tlee10333/Eclectronics-USB/Eclectronics/3dshapes/DFN8_3x3_0.65.step

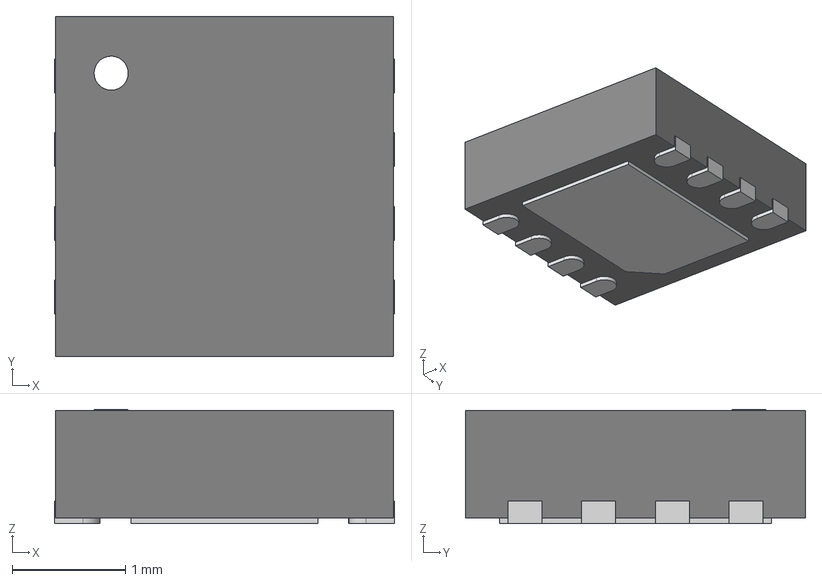
[picture p15: CAD file, 2026-04-13]
Eclectronics/3dshapes/DFN8_3x3_0.65.step
3.00 x 3.00 x 1.01 mm
