tlee10333/Eclectronics-USB/Eclectronics/3dshapes/RP2350A-QFN60.step

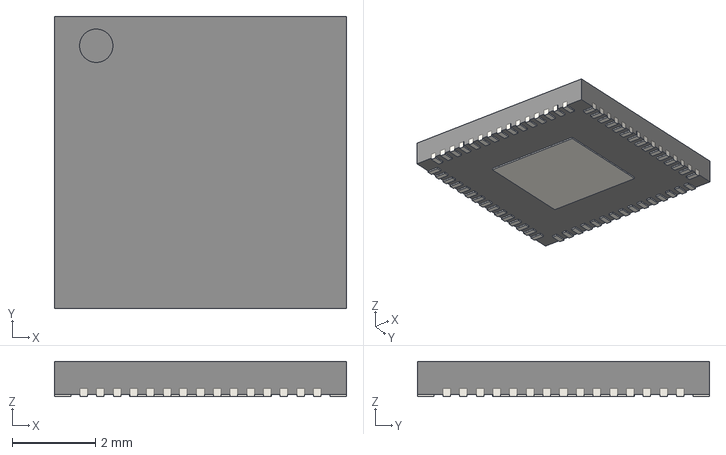
[picture p16: CAD file, 2026-04-13]
Eclectronics/3dshapes/RP2350A-QFN60.step
7.00 x 7.00 x 0.85 mm
