tlee10333/Eclectronics-USB/Eclectronics/3dshapes/BarrelJack.STEP

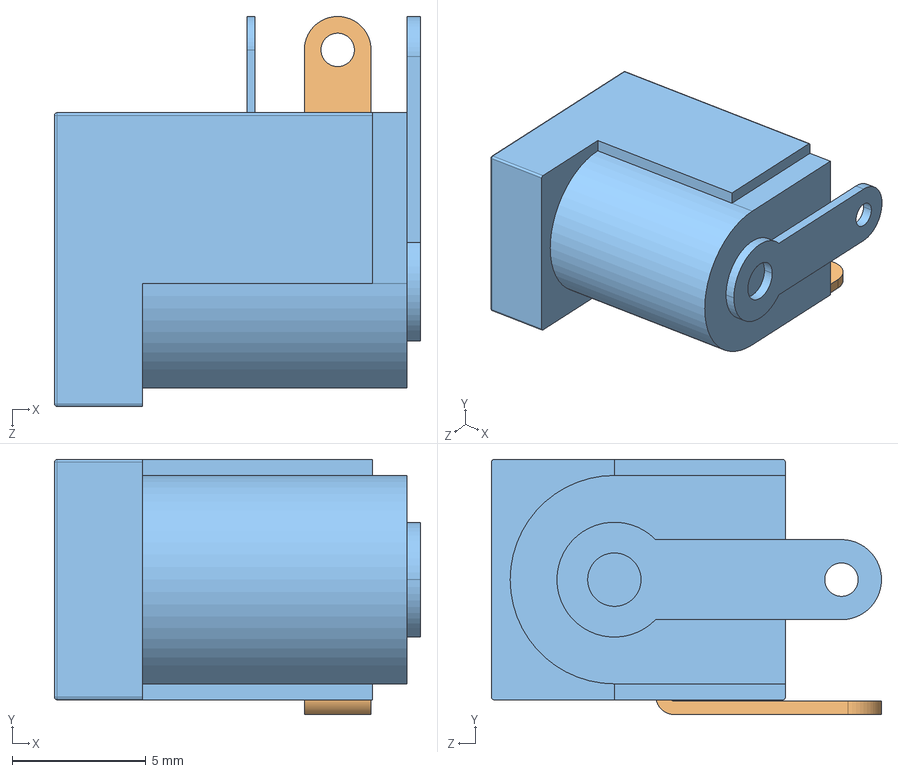
[picture p17: CAD file, 2026-04-13]
Eclectronics/3dshapes/BarrelJack.STEP
13.7 x 9.55 x 14.6 mm
