tlee10333/Eclectronics-USB/Eclectronics/3dshapes/WSON8-6x5.STEP

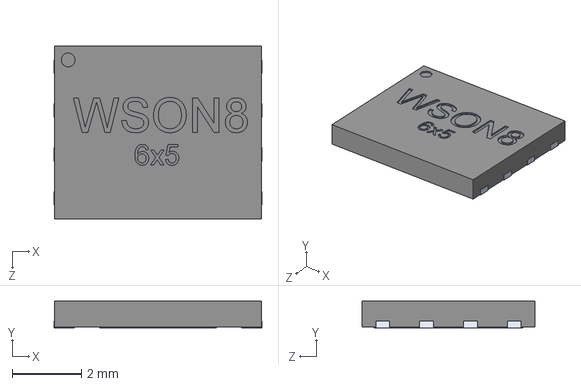
[picture p18: CAD file, 2026-04-13]
Eclectronics/3dshapes/WSON8-6x5.STEP
6.02 x 0.77 x 5.00 mm
