tlee10333/Eclectronics-USB/Eclectronics/3dshapes/RP2040_QFN_PACKAGE.STEP

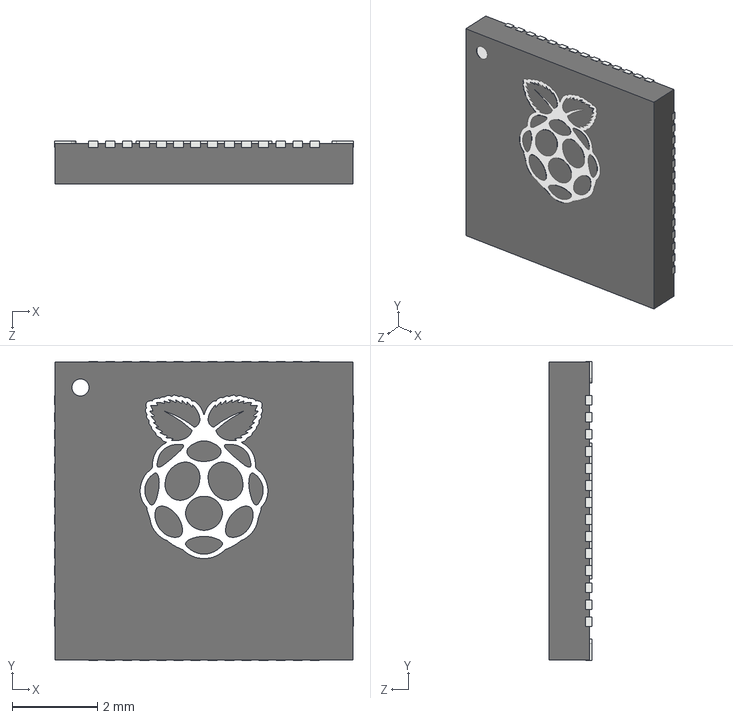
[picture p19: CAD file, 2026-04-13]
Eclectronics/3dshapes/RP2040_QFN_PACKAGE.STEP
7.02 x 7.02 x 1.00 mm
