tlee10333/Eclectronics-USB/Eclectronics/3dshapes/ABM10.STP

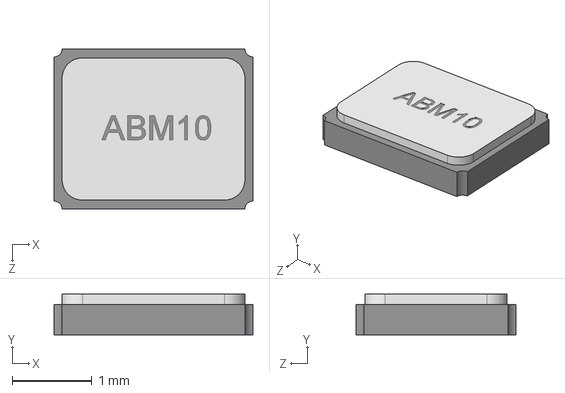
[picture p20: CAD file, 2026-04-13]
Eclectronics/3dshapes/ABM10.STP
2.49 x 0.508 x 2.01 mm
