tlee10333/Eclectronics-USB/Eclectronics/3dshapes/EEEFTH101XAL.step

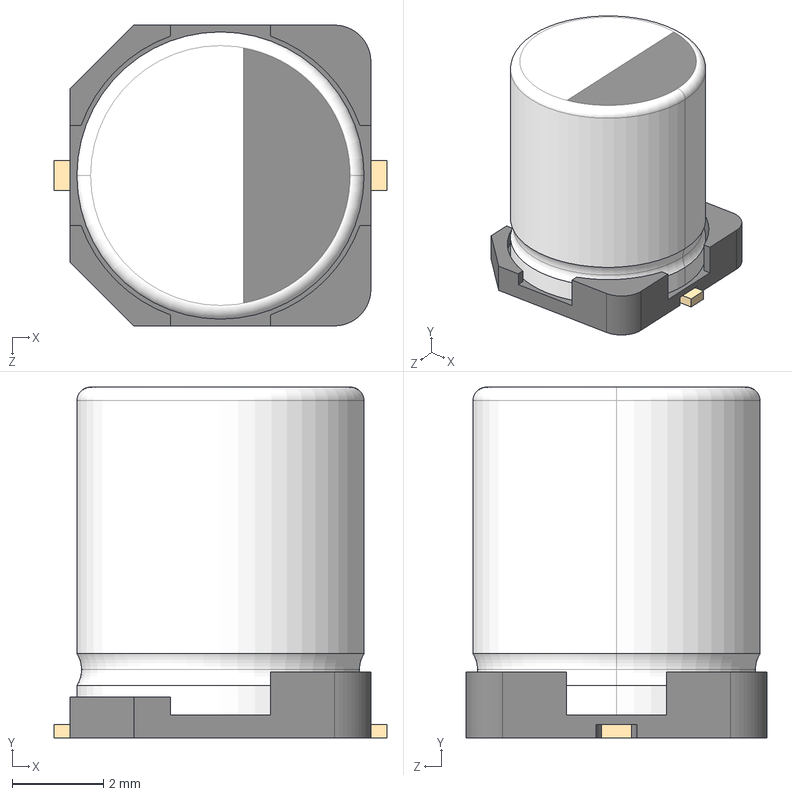
[picture p21: CAD file, 2026-04-13]
Eclectronics/3dshapes/EEEFTH101XAL.step
7.30 x 7.70 x 6.60 mm
