tlee10333/Eclectronics-USB/Eclectronics/3dshapes/IN-S85TATRGB.stp

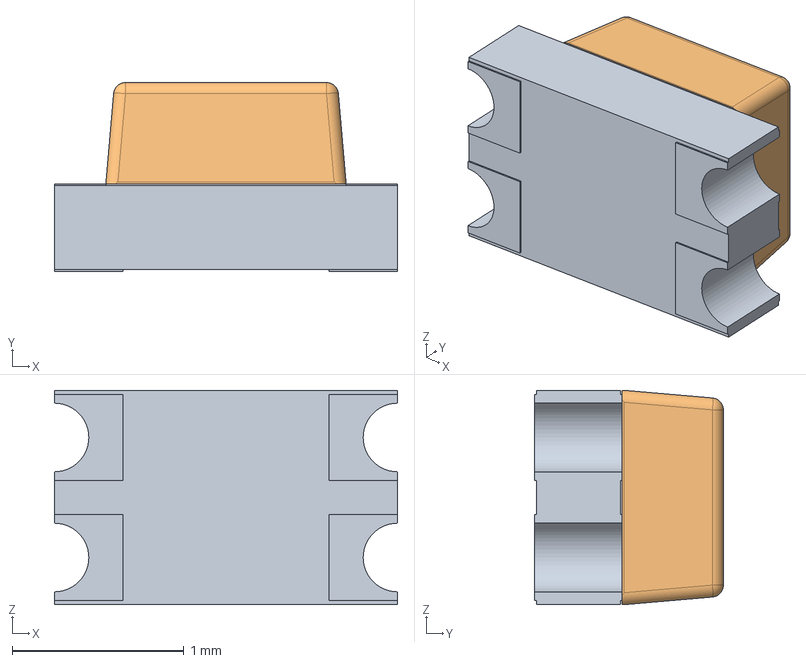
[picture p23: CAD file, 2026-04-13]
Eclectronics/3dshapes/IN-S85TATRGB.stp
2.00 x 1.10 x 1.25 mm
