tlee10333/Eclectronics-USB/Eclectronics/3dshapes/TL3301AFxxxxJ.stp

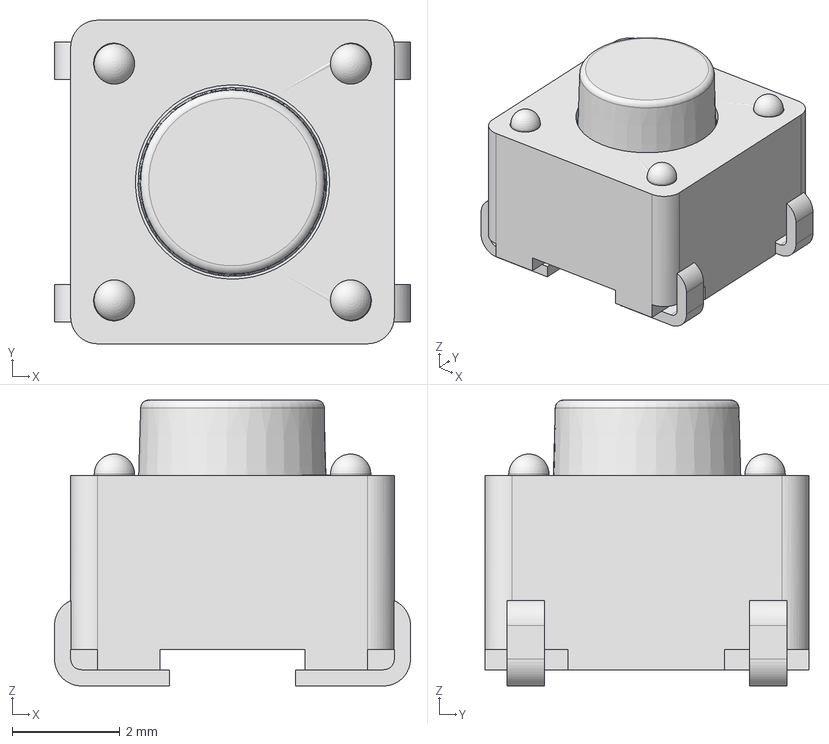
[picture p24: CAD file, 2026-04-13]
Eclectronics/3dshapes/TL3301AFxxxxJ.stp
6.60 x 6.00 x 5.30 mm
