tlee10333/Eclectronics-USB/Eclectronics/3dshapes/219-3M.STEP

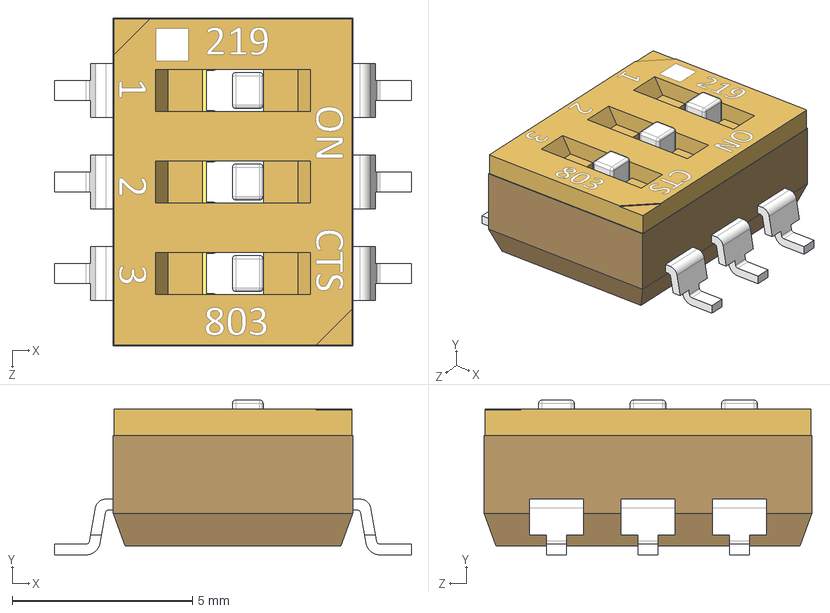
[picture p25: CAD file, 2026-04-13]
Eclectronics/3dshapes/219-3M.STEP
9.91 x 4.30 x 9.10 mm
