tlee10333/Eclectronics-USB/Eclectronics/3dshapes/KXT321LHS.stp

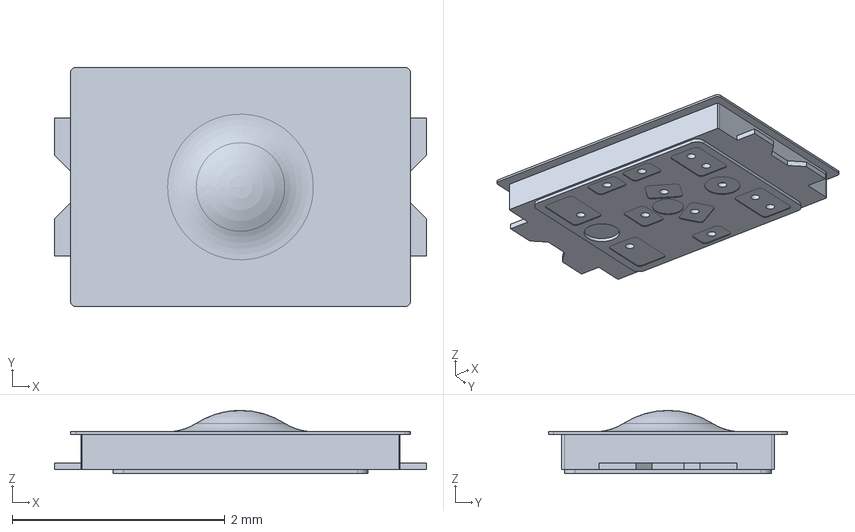
[picture p26: CAD file, 2026-04-13]
Eclectronics/3dshapes/KXT321LHS.stp
3.50 x 2.25 x 0.595 mm
