tlee10333/Eclectronics-USB/Eclectronics/3dshapes/usb4216-03-a.stp

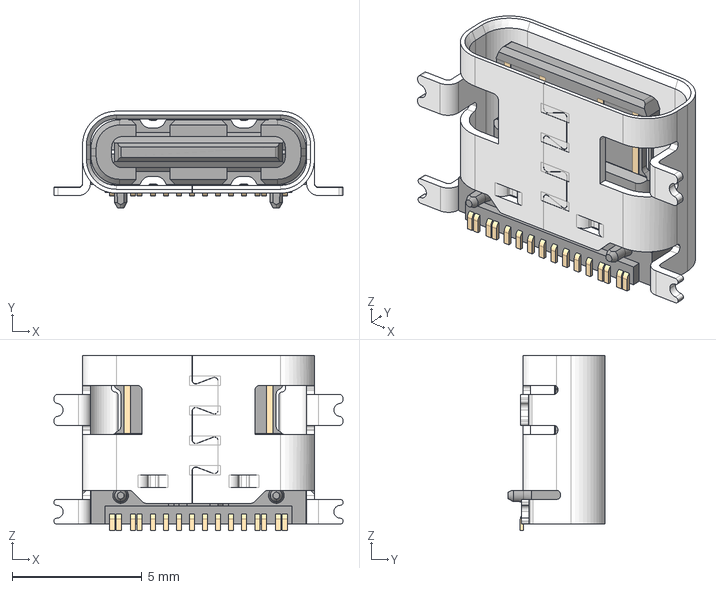
[picture p27: CAD file, 2026-04-13]
Eclectronics/3dshapes/usb4216-03-a.stp
11.1 x 3.73 x 6.75 mm
