tlee10333/Eclectronics-USB/Eclectronics/3dshapes/AOTA-B201610S3R3-101-T.stp

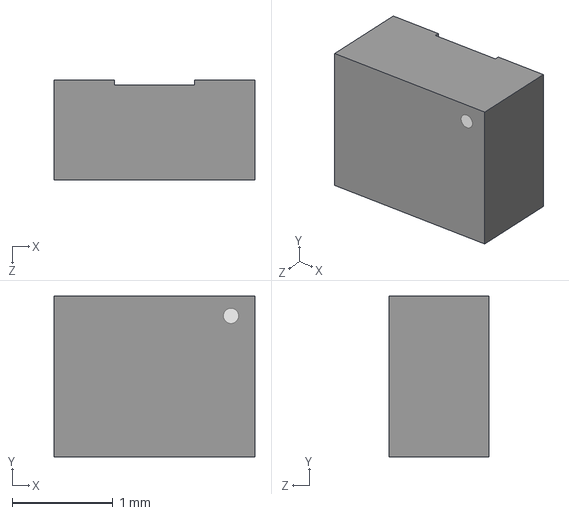
[picture p28: CAD file, 2026-04-13]
Eclectronics/3dshapes/AOTA-B201610S3R3-101-T.stp
2.00 x 1.60 x 1.00 mm
