tlee10333/Eclectronics-USB/Eclectronics/3dshapes/WS2812-2020.STEP

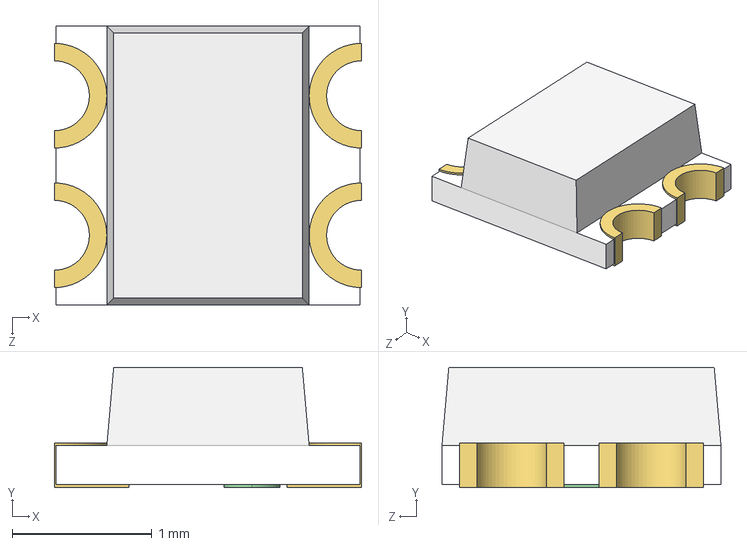
[picture p29: CAD file, 2026-04-13]
Eclectronics/3dshapes/WS2812-2020.STEP
2.20 x 0.86 x 2.00 mm
