tlee10333/Eclectronics-USB/Eclectronics/3dshapes/USB4505-03-0-A_REVA.step

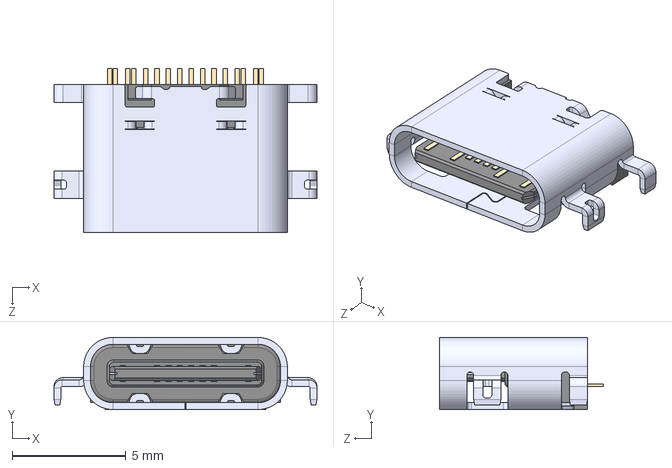
[picture p30: CAD file, 2026-04-13]
Eclectronics/3dshapes/USB4505-03-0-A_REVA.step
11.5 x 3.16 x 7.20 mm
