tlee10333/Eclectronics-USB/Eclectronics/3dshapes/B4B-XH-A.step

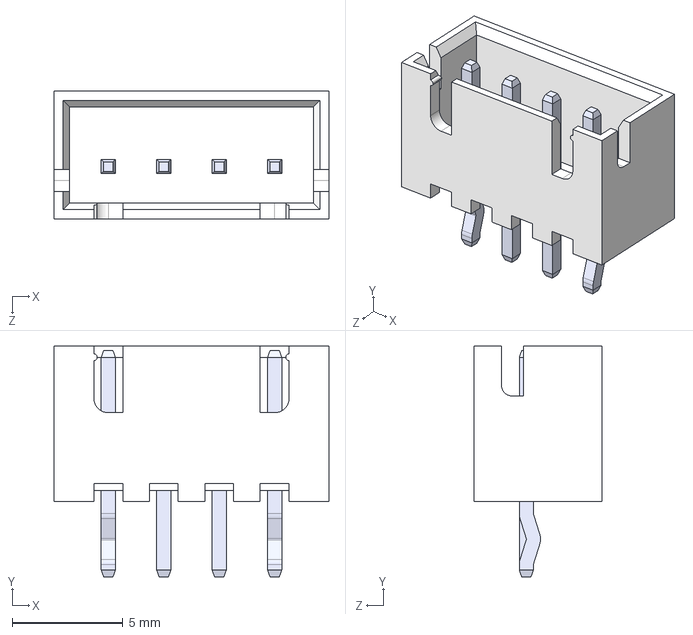
[picture p31: CAD file, 2026-04-13]
Eclectronics/3dshapes/B4B-XH-A.step
12.4 x 10.4 x 5.75 mm
