tlee10333/Eclectronics-USB/Eclectronics/3dshapes/RTE0020A.stp

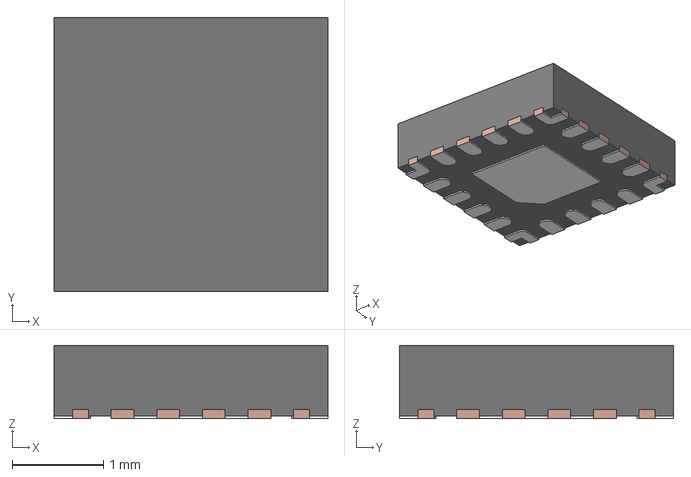
[picture p32: CAD file, 2026-04-13]
Eclectronics/3dshapes/RTE0020A.stp
3.00 x 3.00 x 0.8 mm
FRAME
