tlee10333/Eclectronics-USB/Eclectronics/3dshapes/ABM10-27.000MHZ-E20-T.step

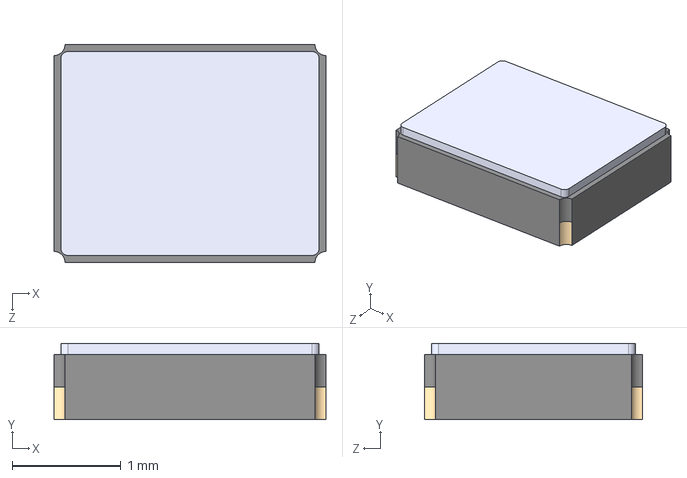
[picture p33: CAD file, 2026-04-13]
Eclectronics/3dshapes/ABM10-27.000MHZ-E20-T.step
2.50 x 0.7 x 2.00 mm
