tlee10333/Eclectronics-USB/Eclectronics/3dshapes/STP_831056289_rev1.stp

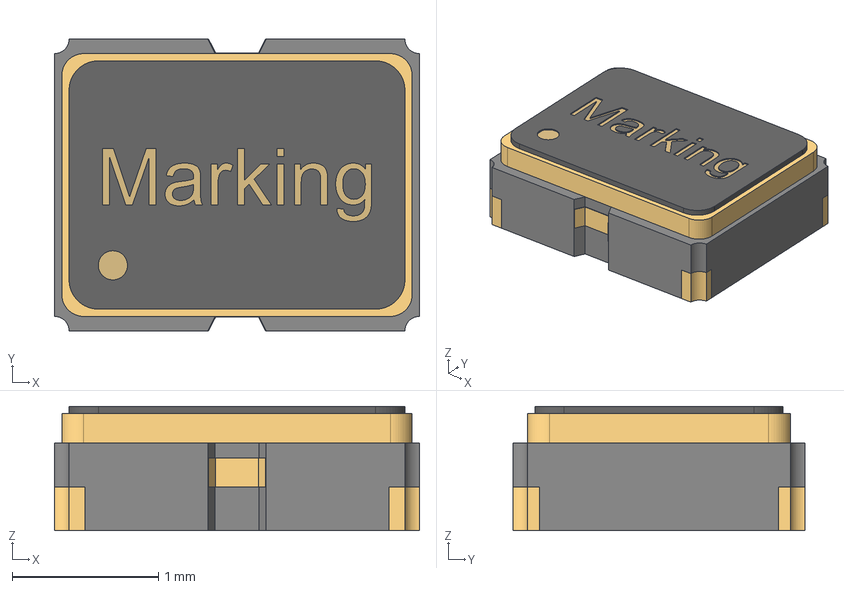
[picture p34: CAD file, 2026-04-13]
Eclectronics/3dshapes/STP_831056289_rev1.stp
2.50 x 2.00 x 0.85 mm
Pins
Cover
