tlee10333/Eclectronics-USB/Eclectronics/3dshapes/CSTNE.step

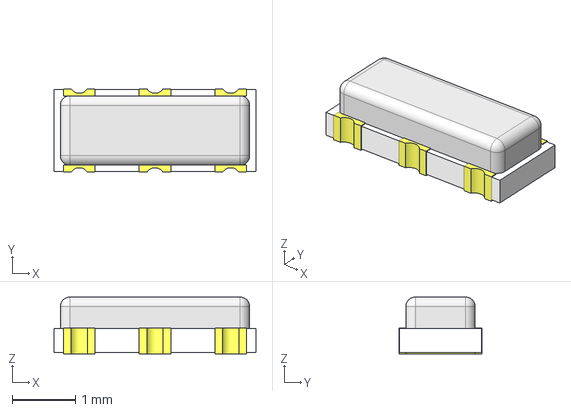
[picture p35: CAD file, 2026-04-13]
Eclectronics/3dshapes/CSTNE.step
3.20 x 1.32 x 0.9 mm
