tlee10333/Eclectronics-USB/Eclectronics/3dshapes/S4B-PH-SM4-TB.stp

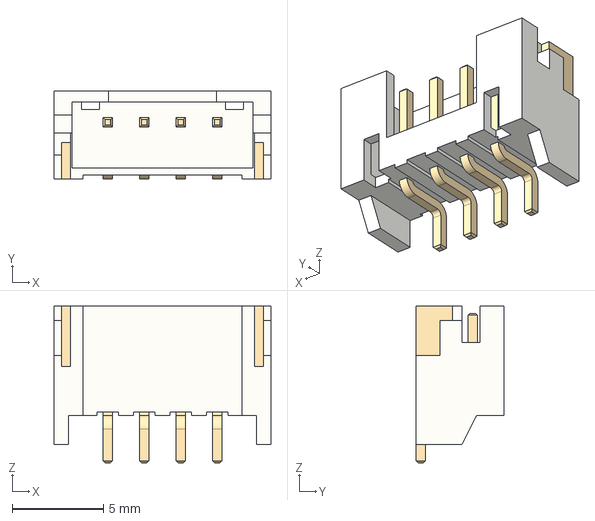
[picture p36: CAD file, 2026-04-13]
Eclectronics/3dshapes/S4B-PH-SM4-TB.stp
11.9 x 4.80 x 8.60 mm
