tlee10333/Eclectronics-USB/Eclectronics/3dshapes/PA5003.182NLT.step

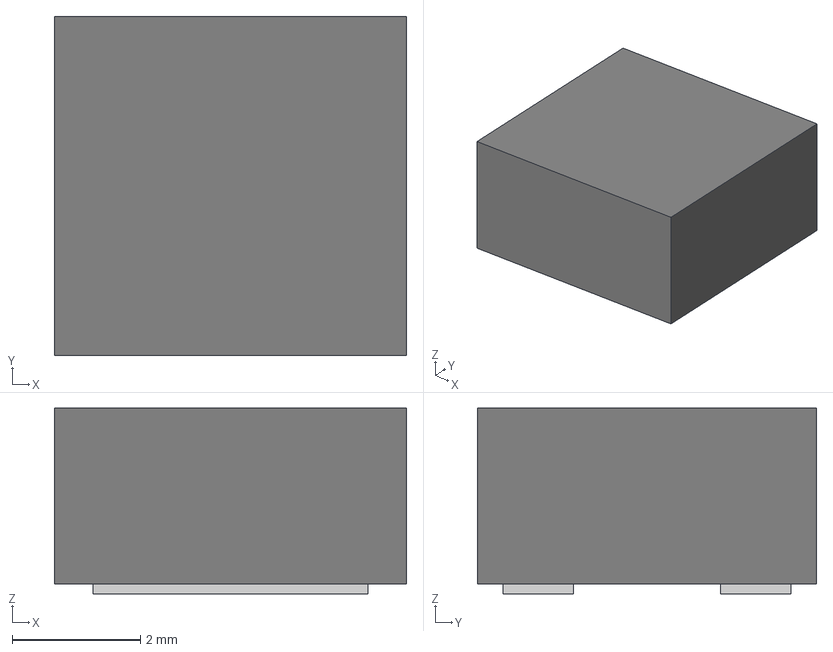
[picture p37: CAD file, 2026-04-13]
Eclectronics/3dshapes/PA5003.182NLT.step
5.50 x 5.30 x 2.90 mm
