tlee10333/Eclectronics-USB/Eclectronics/3dshapes/RNR0011A.stp

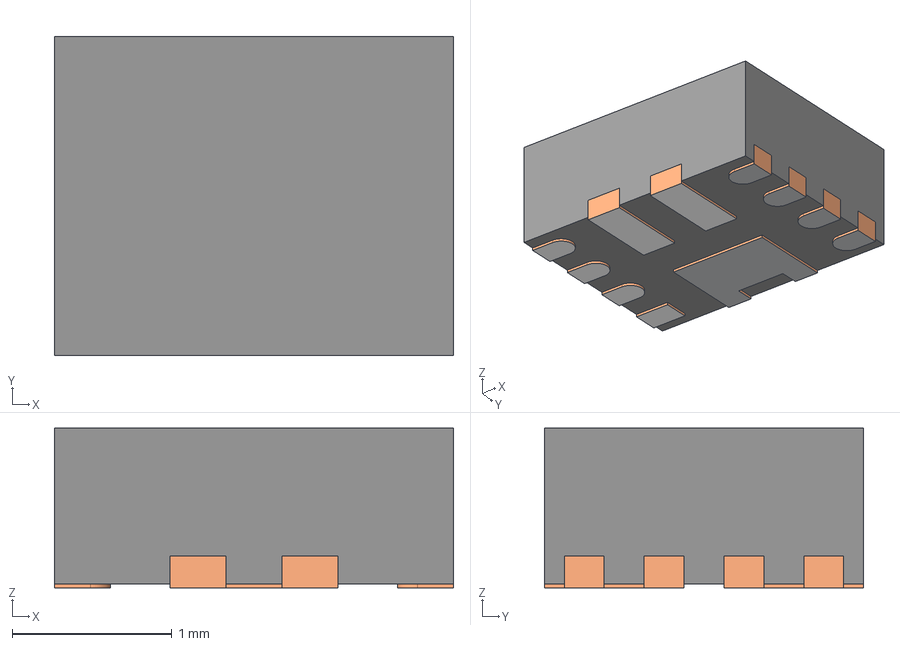
[picture p38: CAD file, 2026-04-13]
Eclectronics/3dshapes/RNR0011A.stp
2.50 x 2.00 x 1.00 mm
FRAME-RNR0011A
BODY-QFN
PIN1-ID
