tlee10333/Eclectronics-USB/Eclectronics/3dshapes/ABS06-107.STP

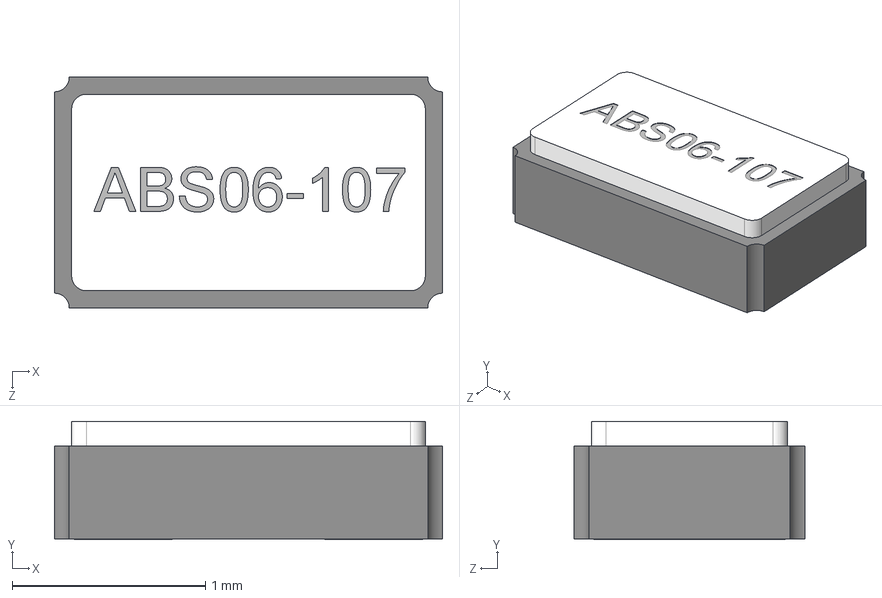
[picture p39: CAD file, 2026-04-13]
Eclectronics/3dshapes/ABS06-107.STP
2.01 x 0.612 x 1.19 mm
