tlee10333/Eclectronics-USB/Eclectronics/3dshapes/SJ-3524-SMT-TR-BE.step

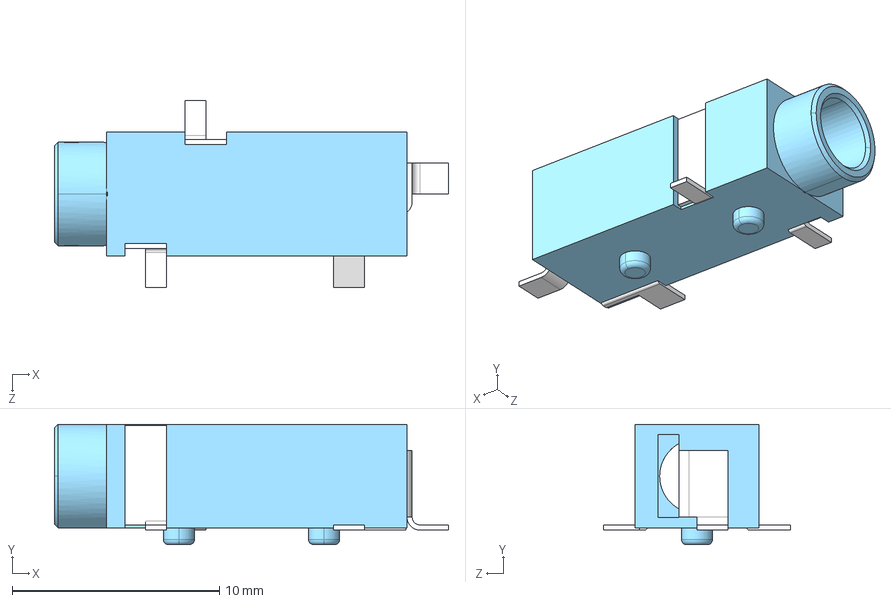
[picture p40: CAD file, 2026-04-13]
Eclectronics/3dshapes/SJ-3524-SMT-TR-BE.step
19.0 x 5.80 x 9.00 mm
