tlee10333/Eclectronics-USB/Eclectronics/3dshapes/3382g-001-xxx.stp

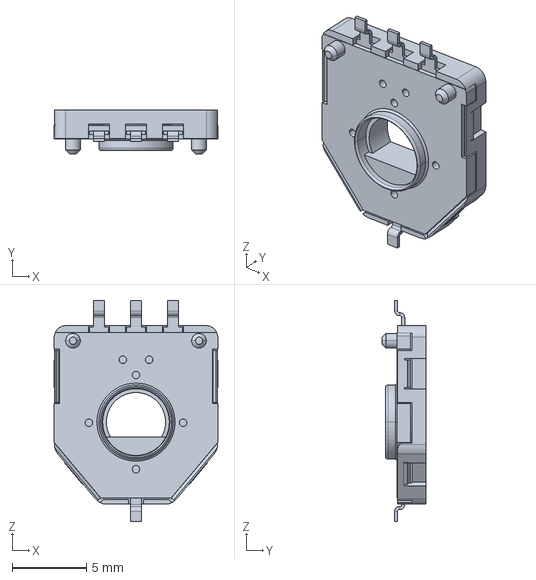
[picture p41: CAD file, 2026-04-13]
Eclectronics/3dshapes/3382g-001-xxx.stp
11.0 x 2.95 x 14.9 mm
