tlee10333/Eclectronics-USB/Eclectronics/3dshapes/USB4105-GF-A.step

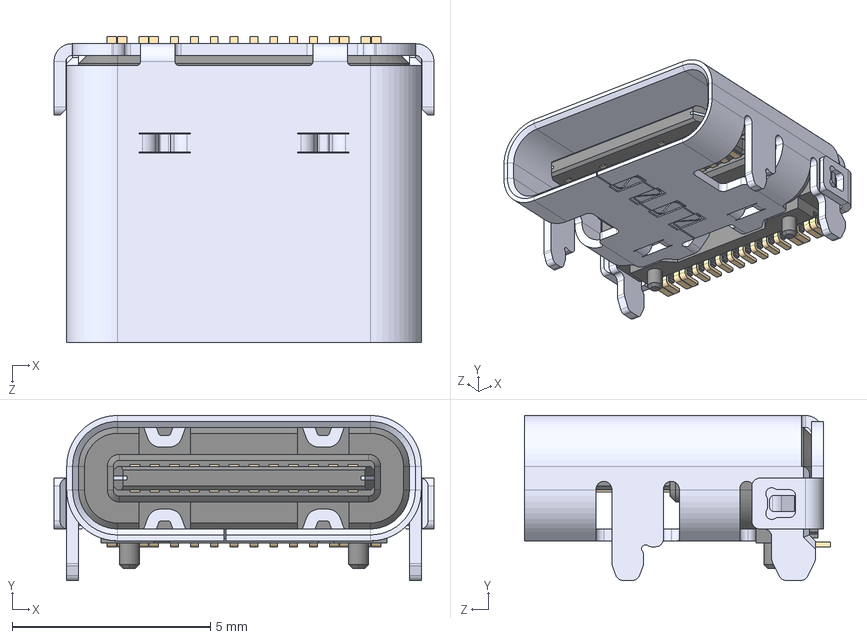
[picture p42: CAD file, 2026-04-13]
Eclectronics/3dshapes/USB4105-GF-A.step
9.58 x 4.16 x 7.71 mm
