tlee10333/Eclectronics-USB/usb_spi/tusb_config.h

#ifndef _TUSB_CONFIG_H_
#define _TUSB_CONFIG_H_

#define CFG_TUSB_MCU OPT_MCU_RP2040
#define CFG_TUSB_RHPORT0_MODE OPT_MODE_DEVICE
#define CFG_TUSB_OS OPT_OS_NONE

#define CFG_TUD_CDC 1

#define CFG_TUD_CDC_RX_BUFSIZE 512
#define CFG_TUD_CDC_TX_BUFSIZE 512

#endif
