tlee10333/Eclectronics-USB/rpi-firmware/modules/pico_usbip_host/src/pio_usb_host_task_stub.c

/*
 * Copyright (c) 2026
 * SPDX-License-Identifier: Apache-2.0
 *
 * Pico-PIO-USB declares this in the header; TinyUSB provides a task loop.
 * Zephyr drives the host via pio_usb_host_frame() on a timer instead.
 */
void pio_usb_host_task(void)
{
}
